regdoug/cicada/cad/solidworks/Lower_Pin_Upper.SLDPRT

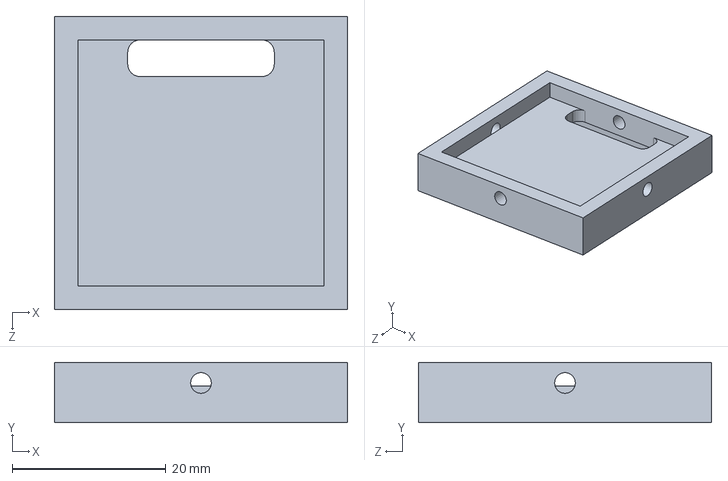
[picture p15: CAD file, 2014-07-29]
cad/solidworks/Lower_Pin_Upper.SLDPRT
38.1 x 7.81 x 38.1 mm
