regdoug/cicada/cad/solidworks/Housing_Base_Male.SLDPRT

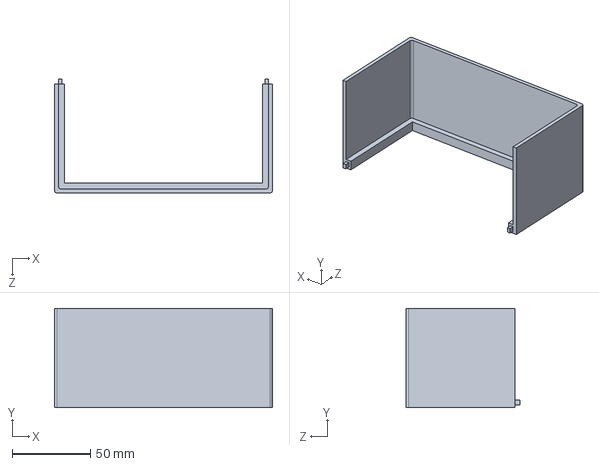
[picture p16: CAD file, 2014-07-29]
cad/solidworks/Housing_Base_Male.SLDPRT
139.7 x 63.5 x 73.0 mm
