regdoug/cicada/cad/solidworks/Electronics_Mounting_Plate_Lower.SLDPRT

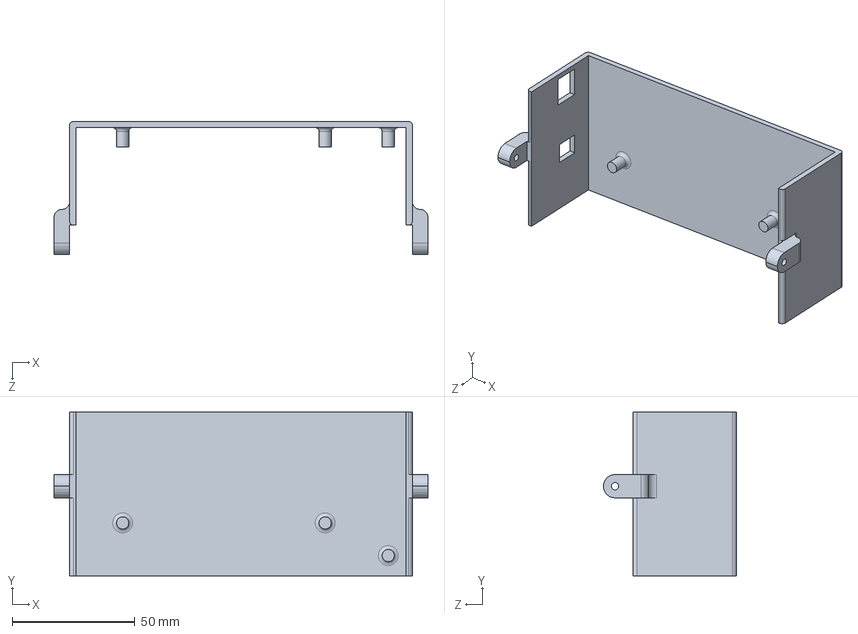
[picture p17: CAD file, 2014-07-29]
cad/solidworks/Electronics_Mounting_Plate_Lower.SLDPRT
152.4 x 66.7 x 54.3 mm
