regdoug/cicada/cad/solidworks/Power_Screw.SLDPRT

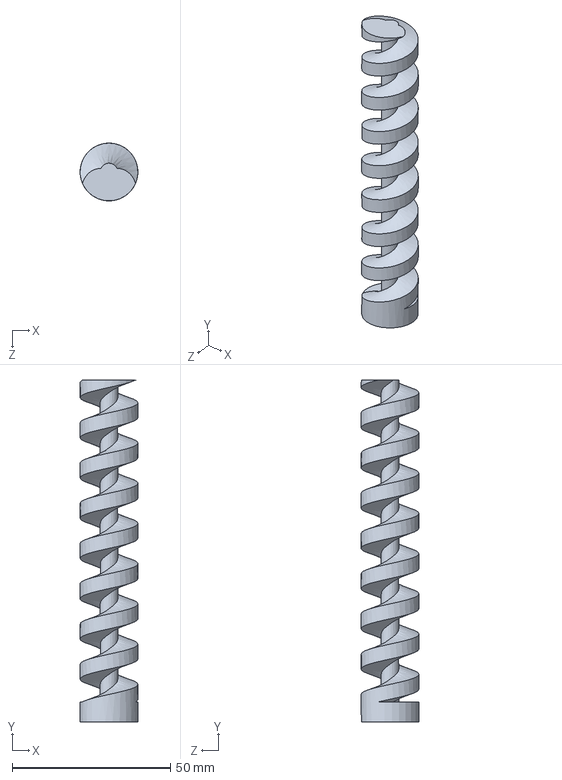
[picture p18: CAD file, 2014-07-29]
cad/solidworks/Power_Screw.SLDPRT
18.3 x 107.9 x 18.3 mm
